imochoa/ergogenesis/hardware/ergogen/output/outlines/wall_ring_ol.dxf

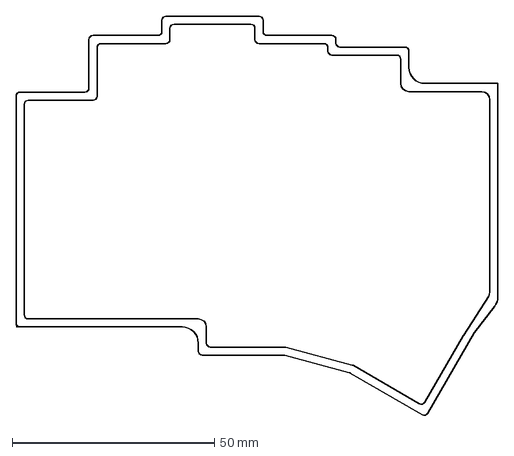
[picture p17: CAD file, 2026-08-10]
hardware/ergogen/output/outlines/wall_ring_ol.dxf
119.0 x 98.7 mm
