imochoa/ergogenesis/hardware/ergogen/output/outlines/bottom_plate_ol.dxf

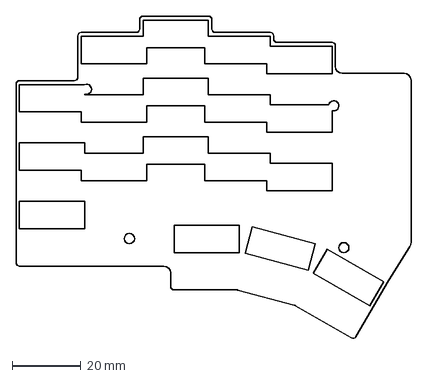
[picture p19: CAD file, 2026-07-27]
hardware/ergogen/output/outlines/bottom_plate_ol.dxf
115.0 x 94.0 mm
