imochoa/ergogenesis/hardware/ergogen/output/outlines/stack_ol.dxf

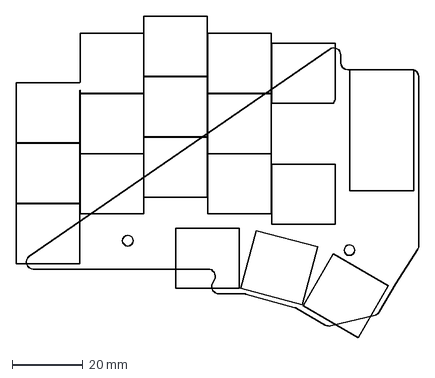
[picture p20: CAD file, 2026-07-27]
hardware/ergogen/output/outlines/stack_ol.dxf
113.4 x 90.5 mm
