imochoa/ergogenesis/hardware/ergogen/output/outlines/board_ol.dxf

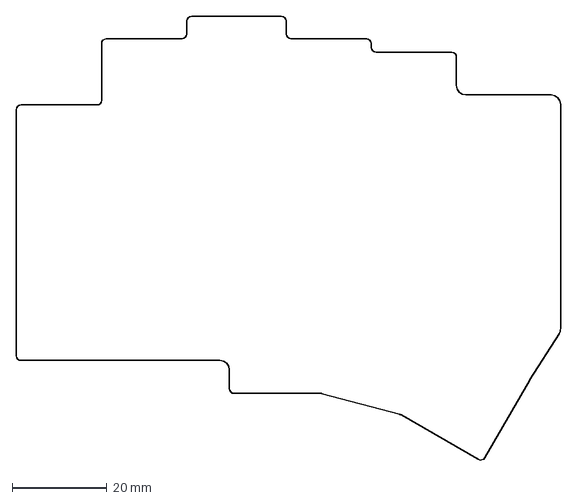
[picture p21: CAD file, 2026-07-25]
hardware/ergogen/output/outlines/board_ol.dxf
115.0 x 94.0 mm
